m24h/sony_ttl_flash/circuit/pcb_3d.png

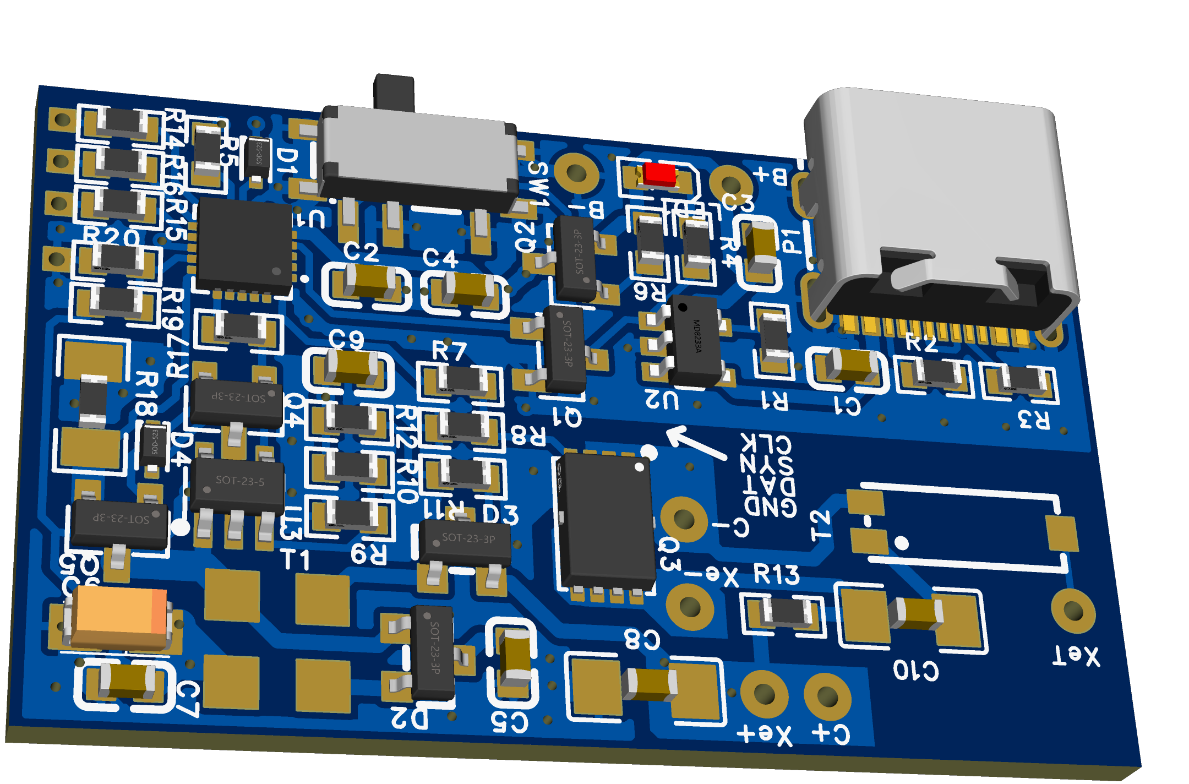
circuit/pcb_3d.png
