m24h/sony_ttl_flash/circuit/pcb_mi.png

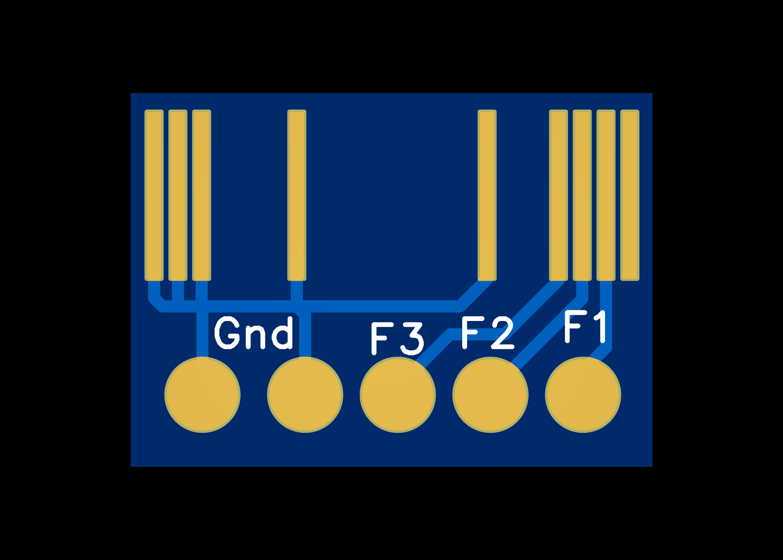
circuit/pcb_mi.png
