m24h/sony_ttl_flash/circuit/pcb_top2.png

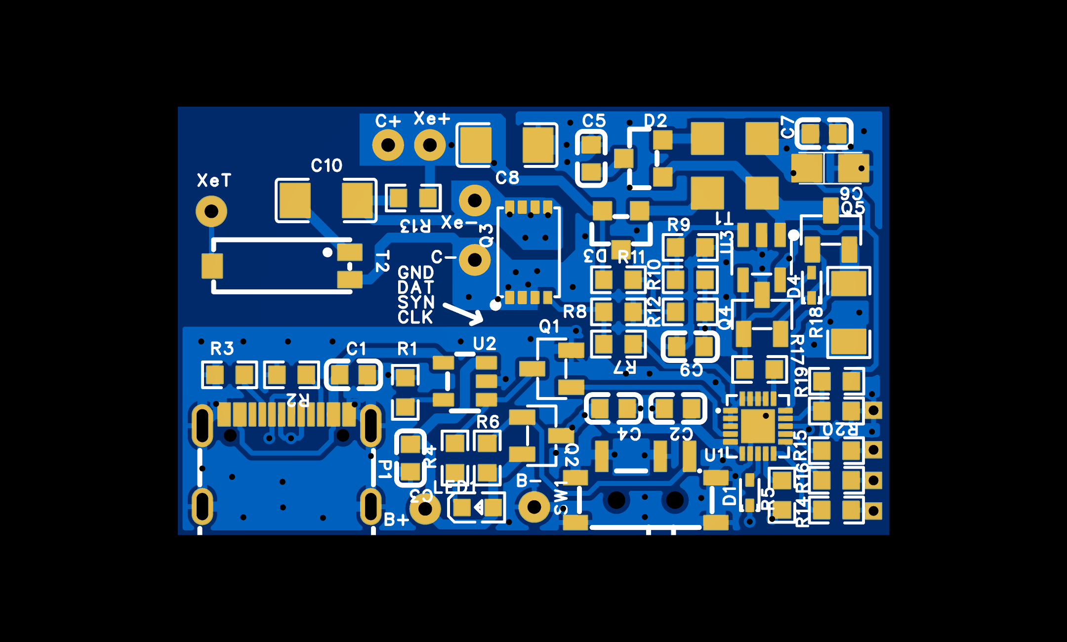
circuit/pcb_top2.png
