m24h/sony_ttl_flash/circuit/pcb_top.png

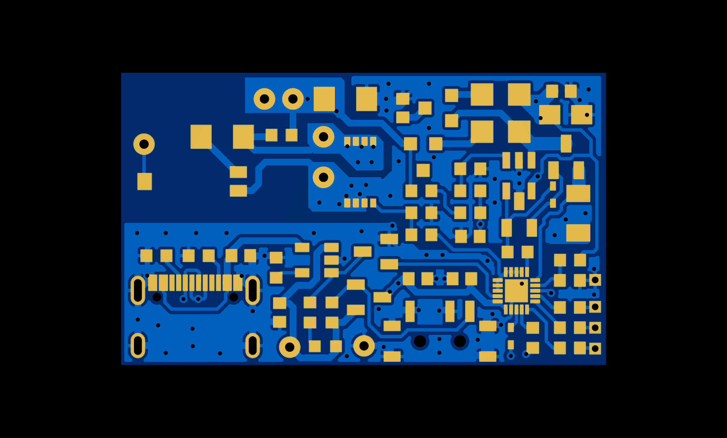
circuit/pcb_top.png
