m24h/sony_ttl_flash/practice/asymble.jpg

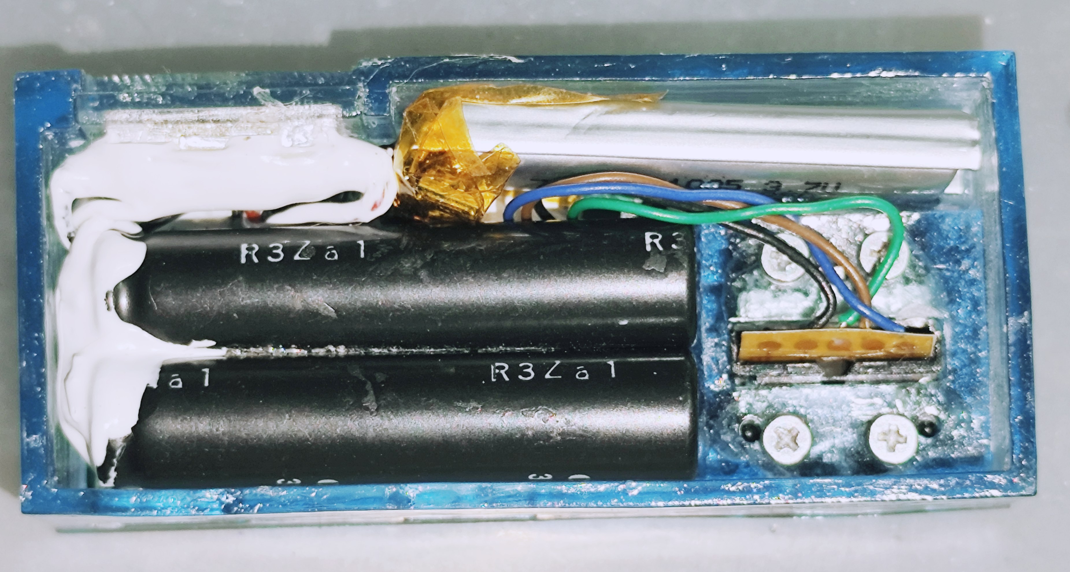
practice/asymble.jpg
