m24h/sony_ttl_flash/practice/on_camera.jpg

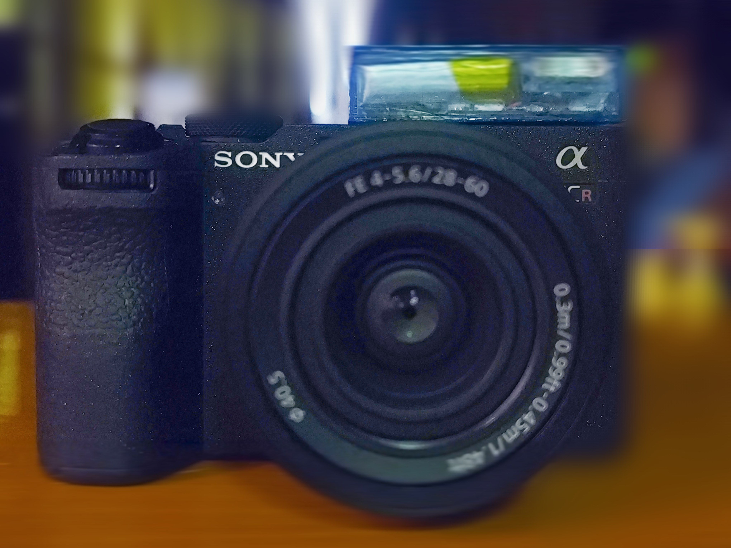
practice/on_camera.jpg
