m24h/sony_ttl_flash/practice/on_my_hand.jpg

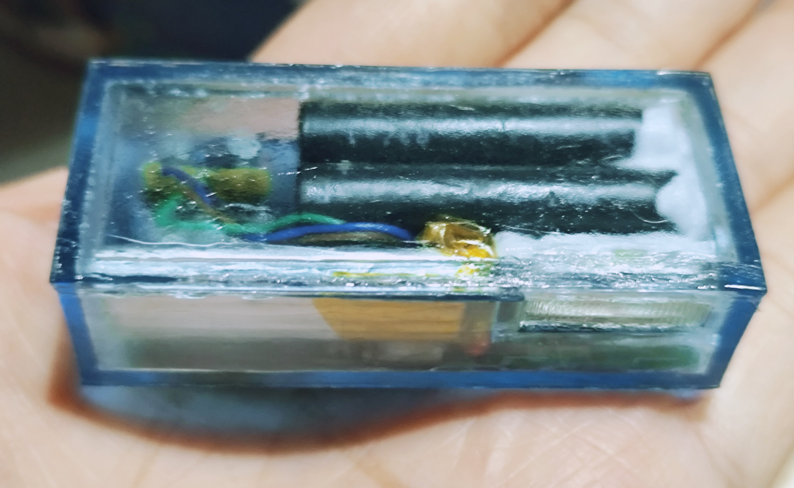
practice/on_my_hand.jpg
